SindreKvam/fault-injection-demo/sim/comparator_circuit/Comparator.asc

R1: Res; 10k
U1: TLV6001
V1: Voltage; PULSE(0 3.3 0 0 0 3e-6 10e-6)
V2: Voltage; 2.5V
V3: Voltage; 5V
Named nets: 0, Vin, Vout
.tran 10us
